schuyler4/USB_Curve_Tracer/examples/1N4001_REV2.png

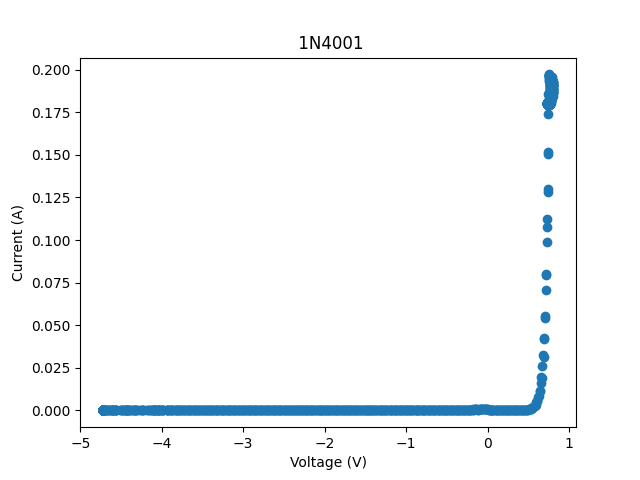
examples/1N4001_REV2.png
