schuyler4/USB_Curve_Tracer/examples/1N4001_REV3_LM324.png

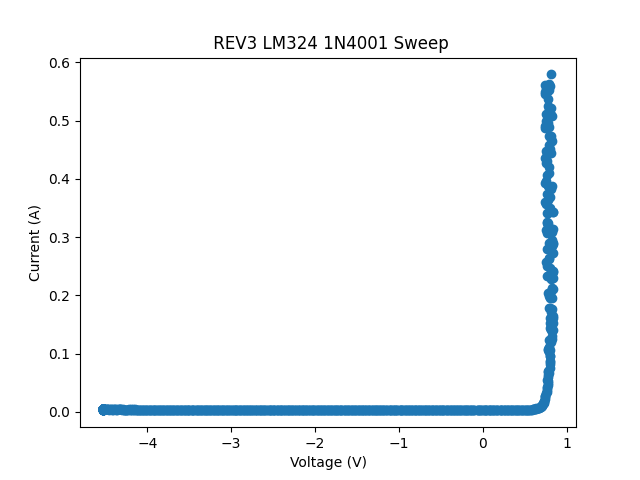
examples/1N4001_REV3_LM324.png
