schuyler4/USB_Curve_Tracer/examples/TIP122G_REV3_LM324.png

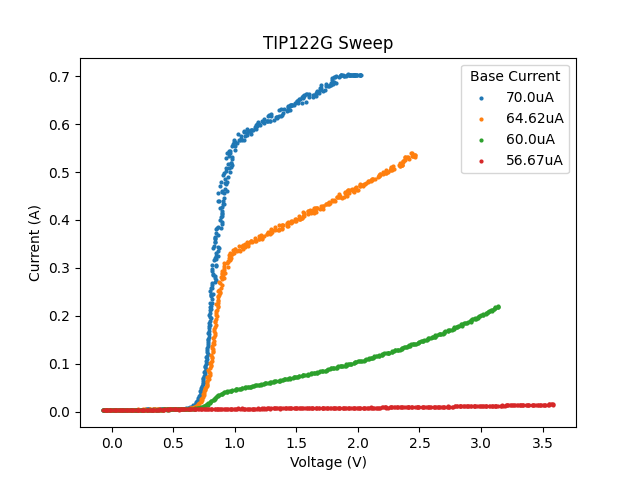
examples/TIP122G_REV3_LM324.png
