schuyler4/USB_Curve_Tracer/examples/zener_diode_plot_REV2.png

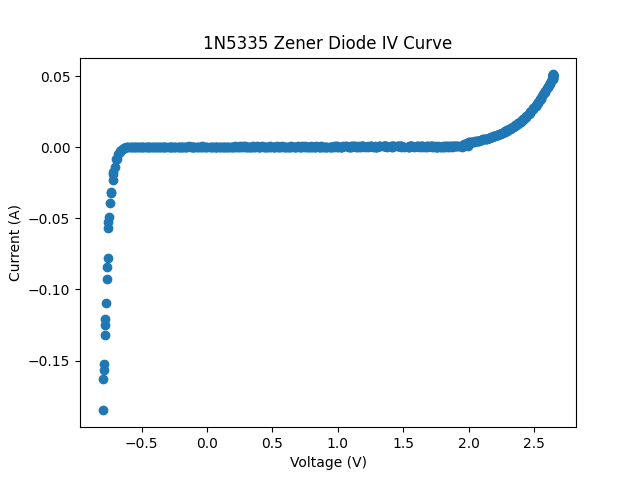
examples/zener_diode_plot_REV2.png
