schuyler4/USB_Curve_Tracer/REV3_Picture_PCB.JPG

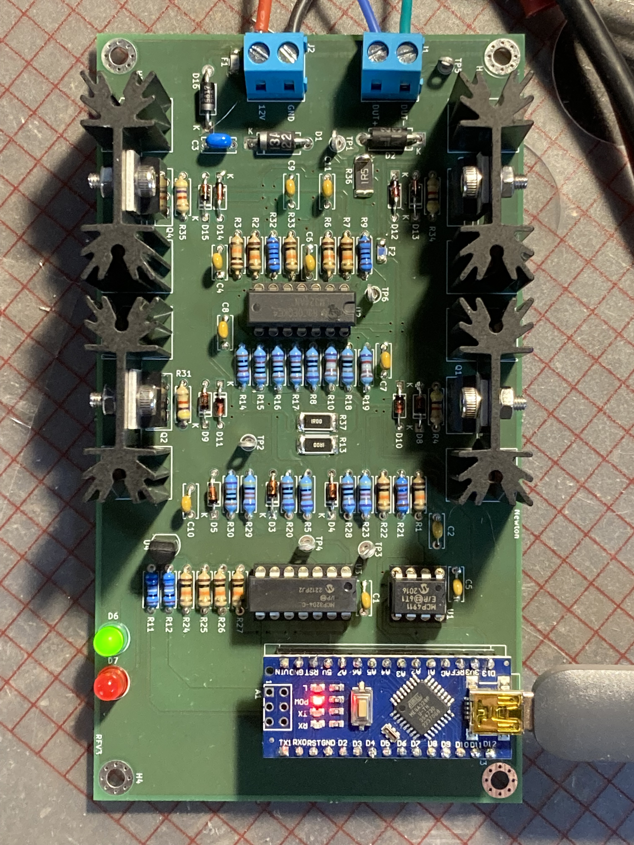
REV3_Picture_PCB.JPG
