schuyler4/USB_Curve_Tracer/test/step_averaging/ZVN3310A/ZVN3310A.png

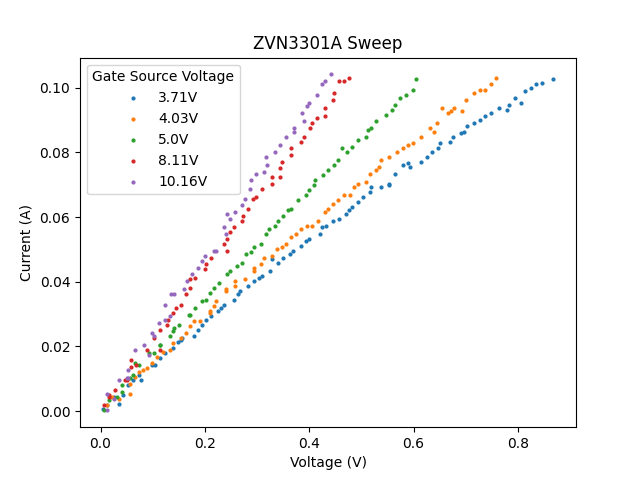
test/step_averaging/ZVN3310A/ZVN3310A.png
