schuyler4/USB_Curve_Tracer/test/rev2_test/test_plot/33.png

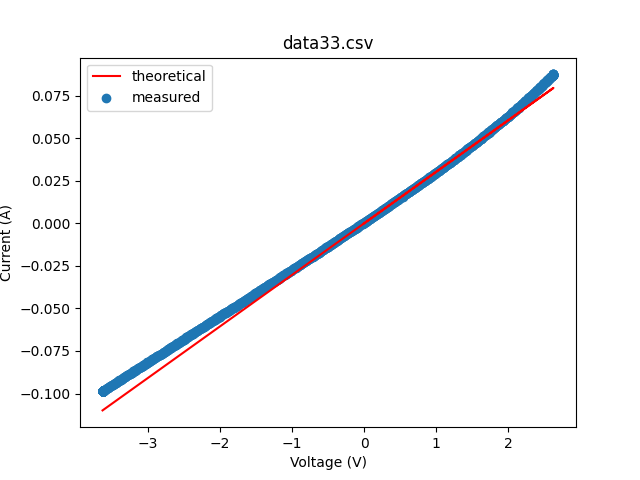
test/rev2_test/test_plot/33.png
