schuyler4/USB_Curve_Tracer/test/rev3_diode_comparison_test/1N4001_comparison.png

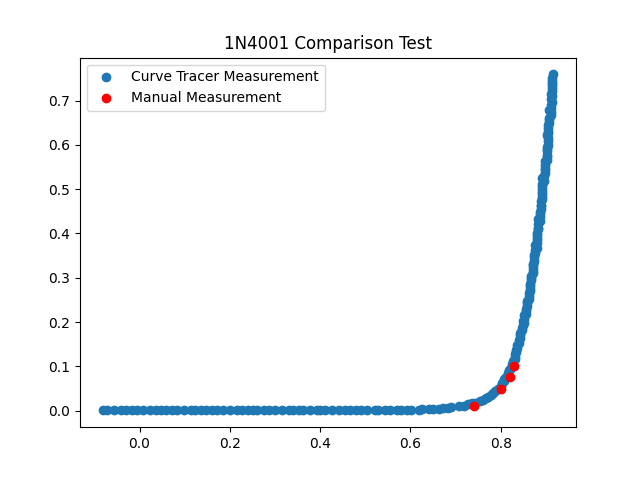
test/rev3_diode_comparison_test/1N4001_comparison.png
