schuyler4/USB_Curve_Tracer/test/rev3_scope_comparison/1N4148_scope_comparison.png

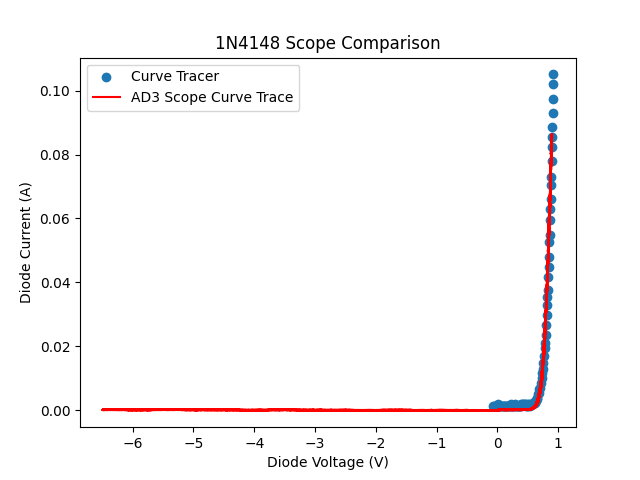
test/rev3_scope_comparison/1N4148_scope_comparison.png
