schuyler4/USB_Curve_Tracer/test/rev3_test_LM324/resistor_test/test_plot/470.png

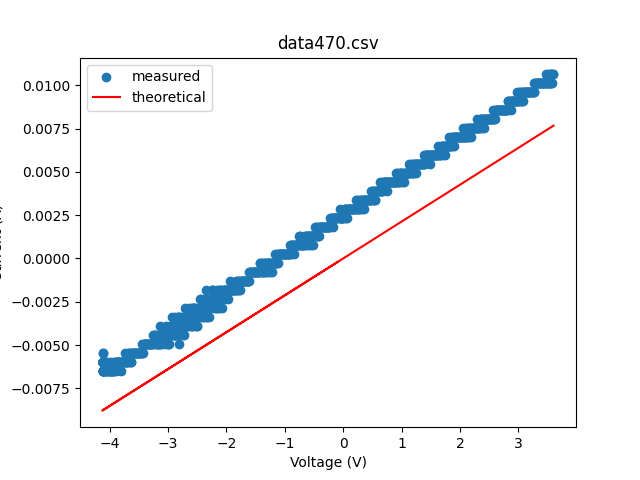
test/rev3_test_LM324/resistor_test/test_plot/470.png
