schuyler4/USB_Curve_Tracer/test/rev3_test_LMC6484/resistor_test/test_plot/460.png

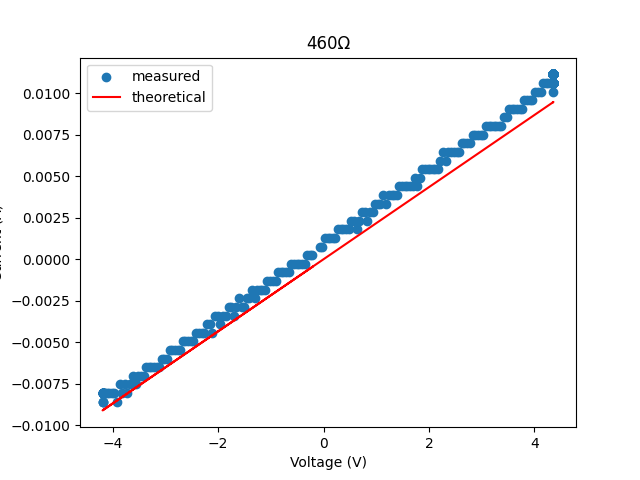
test/rev3_test_LMC6484/resistor_test/test_plot/460.png
