schuyler4/USB_Curve_Tracer/test/step_averaging/test_plot/470.png

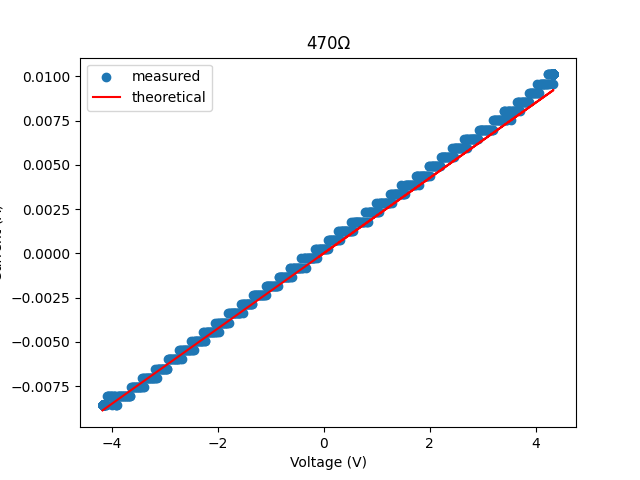
test/step_averaging/test_plot/470.png
