schuyler4/USB_Curve_Tracer/test/various_op_amps/TLC2274IN.png

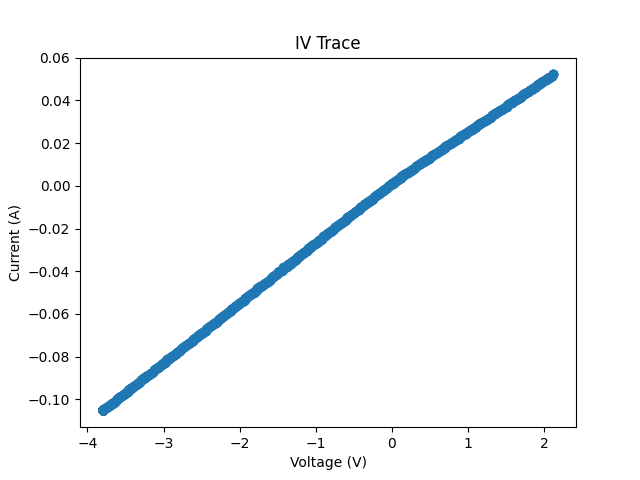
test/various_op_amps/TLC2274IN.png
