schuyler4/USB_Curve_Tracer/electronics/rev3/simulation/Draft1.asc

D1: diode; 1N4148
D2: diode; 1N4148
D3: diode; 1N4148
D4: diode; 1N4148
I1: current; 1A
Q1: npn; 2N2222
Q2: npn; 2N2222
Q3: pnp; 2N2907
Q4: pnp; 2N2907
R1: res; 4.7k
R2: res; 4.7k
R3: res; 1k
U1: UniversalOpAmp
V1: voltage; 12V
V2: signal; SINE(6 1 1K)
V3: voltage; 12V
Named nets: 0
.tran 10ms
