schuyler4/USB_Curve_Tracer/electronics/rev3/simulation/V2_Stage.asc

D1: diode
D2: diode
Q1: npn; 2N2222
Q2: pnp; 2N2907
Q3: npn; 2N3055
Q4: pnp; D45H11
R1: res; 1k
R2: res; 100
R3: res; 0.01
R5: res; 100
R6: res; 1k
R7: res; 0.01
R8: res; 100
U1: UniversalOpAmp
U2: UniversalOpAmp
V1: voltage; 6V
V2: voltage; 6V
V3: signal; SINE(0 3V 100)
V4: voltage; 6V
V5: voltage; 6V
V6: voltage; 6V
V7: signal; SINE(0 3V 100)
V8: voltage; 6V
V9: voltage; 6V
V10: voltage; 6V
Named nets: 0
.tran 10m
