schuyler4/USB_Curve_Tracer/software/interface.py

'''
FILENAME: interface.py

description: This file takes care of the serial communication with the curve tracer and the command line interface.

Written by Marek Newton
'''

from enum import Enum

import serial
import time
import csv
import numpy as np

from . import constants
from .plot import plot_data
from .IV import calculate_max_current_code, split_adc_code


class DirectionalMode(Enum):
    BIDIRECTIONAL = 0
    UNIDIRECTIONAL = 1


def init_serial():
    try:
        my_serial = serial.Serial()
        my_serial.port = constants.SERIAL_PORT
        my_serial.baudrate = constants.BAUDRATE
        my_serial.timeout = constants.SECOND_DELAY
        
        my_serial.open()
        # For some reason, a delay is required before flushing the serial buffer.
        time.sleep(constants.SECOND_DELAY)
        my_serial.flush()
        # Another delay is required after flushing the serial buffer, before using the serial port.
        time.sleep(constants.SECOND_DELAY)
        return my_serial
    except:
        print(constants.OPENING_ERROR)
        return None


def read_serial_data(my_serial):
    no_data_count = 0
    received_data = []
    logging_data = False

    while True: 
        try:
            data_str = my_serial.readline().decode(constants.DECODING_SCHEME)

            if(data_str == ''):
                no_data_count += 1

                if(no_data_count > constants.NO_DATA_ERROR_COUNT):
                    print(constants.NO_DATA_ERROR)
                    break
            elif(constants.DATA_END_COMMAND in data_str):
                logging_data = False
                break
            elif(constants.DATA_START_COMMAND in data_str):
                logging_data = True
            elif(logging_data):
                received_data.append(data_str)
                no_data_count = 0
        except:
            print(constants.DATA_READ_ERROR)
            break   

    time.sleep(constants.SECOND_DELAY)

    return received_data


def sanitize_string(string):
    cleaned_string = string.replace(constants.TRANSMIT_STRING_GARBAGE, '').replace(constants.NEWLINE, '')
    return cleaned_string

 
def get_data_codes(data):
    if(constants.POWER_DISCONNECTED in sanitize_string(data[0])):
        return [], [], False
    else:
        codes = []
        for datum in data:  
            point = datum.split(constants.COMMA)
            point[0] = int(sanitize_string(point[0]))
            point[1] = int(sanitize_string(point[1]))
            codes.append(point)
        codes = np.array(codes)
        current_codes = codes[:,0]
        voltage_codes = codes[:,1]
        return current_codes, voltage_codes, True


def sweep_device_command(my_serial):
    my_serial.write(constants.SWEEP_PROCESSOR_COMMAND)
    time.sleep(constants.DATA_RECEIVE_DELAY)
    data = read_serial_data(my_serial)
    return data


def change_mode_command(my_serial, processor_mode):
    my_serial.write(processor_mode)
    time.sleep(constants.DATA_RECEIVE_DELAY)


def write_data_to_CSV(current_codes, voltage_codes, title):
    csv_filename = title + constants.CSV_EXTENSION
    csv_data = []
    for index, current_code in enumerate(current_codes):
        csv_data.append([current_code, voltage_codes[index]])
    
    with open(csv_filename, constants.FILE_WRITE) as fp:
        writer = csv.writer(fp, delimiter = constants.COMMA)
        writer.writerows(csv_data)


def enter_current_limit(my_serial, hardware_revision, directional_mode):
    if(directional_mode == DirectionalMode.BIDIRECTIONAL):
        print(constants.CURRENT_LIMIT_UNIDIRECTIONAL)
        
    while True:
        current_limit = input(constants.CURRENT_LIMIT_PROMPT)
        try:
            current_limit = float(current_limit)

            if(current_limit > constants.MAXIMUM_USER_CURRENT_LIMIT or current_limit < 0):
                raise ValueError
            
            # The UART peripheral only works with 8 bit values, so it is convient to 
            # split the current code into two bytes and transmit them one at a time.
            current_code = calculate_max_current_code(current_limit, hardware_revision)
            upper_current_code, lower_current_code = split_adc_code(current_code)

            print('current code:', current_code)
            print('upper current code', upper_current_code)
            print('lower current code', lower_current_code)

            # Transmission (Most Significant Byte First)
            my_serial.write(constants.CURRENT_LIMIT_PROCESSOR_COMMAND)
            time.sleep(constants.SECOND_DELAY)
            my_serial.write(upper_current_code.to_bytes(1, byteorder='big'))
            time.sleep(constants.SECOND_DELAY)
            my_serial.write(lower_current_code.to_bytes(1, byteorder='big'))

            for _ in range(0, constants.ACK_READ_ATTEMPTS):
                ack = my_serial.readline().decode(constants.DECODING_SCHEME)
                print(ack)
                if(constants.CURRENT_LIMIT_ACK in ack):
                    print("current limit ack", ack)
                    break
            break
        except ValueError:
            print(constants.INVALID_CURRENT_LIMIT)


def max_current_limit(my_serial):
    my_serial.write(constants.MAX_CURRENT_LIMIT_PROCESSOR_COMMAND)
    time.sleep(constants.DATA_RECEIVE_DELAY)


def user_interface(my_serial):
    current_codes = []
    voltage_codes = []
    title = None
    hardware_revision = 3
    directional_mode = DirectionalMode.BIDIRECTIONAL

    print(constants.COMPONENT_CONNECTION_MESSAGE)

    while True:
        user_input = input(constants.COMMAND_PROMPT)
        command_exists = constants.SWEEP_USER_COMMAND in user_input

        if(command_exits and user_input != constants.SWEEP_USER_COMMAND):
            command_and_title = user_input.split(constants.COMMA)
            if(len(command_and_title) != constants.TITLE_COMMAND_LIST_LENGTH):
                print(constants.INVALID_COMMAND_ERROR)
                continue
            data = sweep_device_command(my_serial)
            current_codes, voltage_codes, power_connected = get_data_codes(data)
            if(power_connected):
                plot_data(current_codes, 
                          voltage_codes, 
                          command_and_title[1], 
                          hardware_revision).show()
            else:
                print(constants.POWER_DISCONNECTED_ERROR)
                break

        elif(user_input == constants.SWEEP_USER_COMMAND):
            data = sweep_device_command(my_serial)
            current_codes, voltage_codes, power_connected = get_data_codes(data)
            if(power_connected):
                plot_data(current_codes, 
                          voltage_codes, 
                          constants.IV_TRACE_TITLE,
                          hardware_revision).show()
            else:
                print(constants.POWER_DISCONNECTED_ERROR)
                break

        elif(user_input == constants.CSV_USER_COMMAND):
            if(len(current_codes) == 0 and len(voltage_codes) == 0):
                print(constants.STORED_SWEEPS_ERROR)
                continue
            else:
                title = input(constants.TITLE_PROMPT)
                write_data_to_CSV(current_codes, voltage_codes, title)

        elif(user_input == constants.UNIDIRECTIONAL_USER_COMMAND):
            change_mode_command(my_serial, constants.UNIDIRECTIONAL_PROCESSOR_COMMAND)
            directional_mode = DirectionalMode.UNIDIRECTIONAL

        elif(user_input == constants.BIDIRECTIONAL_USER_COMMAND):
            change_mode_command(my_serial, constants.BIDIRECTIONAL_PROCESSOR_COMMAND)
            directional_mode = DirectionalMode.BIDIRECTIONAL

        elif(user_input == constants.REV1_USER_COMMAND):
            hardware_revision = 1
        
        elif(user_input == constants.REV2_USER_COMMAND):
            hardware_revision = 2

        elif(user_input == constants.CURRENT_LIMIT_COMMAND):
            enter_current_limit(my_serial, hardware_revision, directional_mode)
            change_mode_command(my_serial, constants.UNIDIRECTIONAL_PROCESSOR_COMMAND)
            directional_mode = DirectionalMode.UNIDIRECTIONAL

        elif(user_input == constants.MAXIMUM_USER_CURRENT_LIMIT):
            max_current_limit(my_serial)
            change_mode_command(my_serial, constants.BIDIRECTIONAL_PROCESSOR_COMMAND)
            directional_mode = DirectionalMode.BIDIRECTIONAL
                    
        elif(user_input == constants.EXIT_USER_COMMAND):
            break
        else:
            print(constants.INVALID_COMMAND_ERROR)
